MMDavito/8_switch_rgb/KiCad/8_switch_rgb_pcb_revision_1/3D_no_grund_plane.png

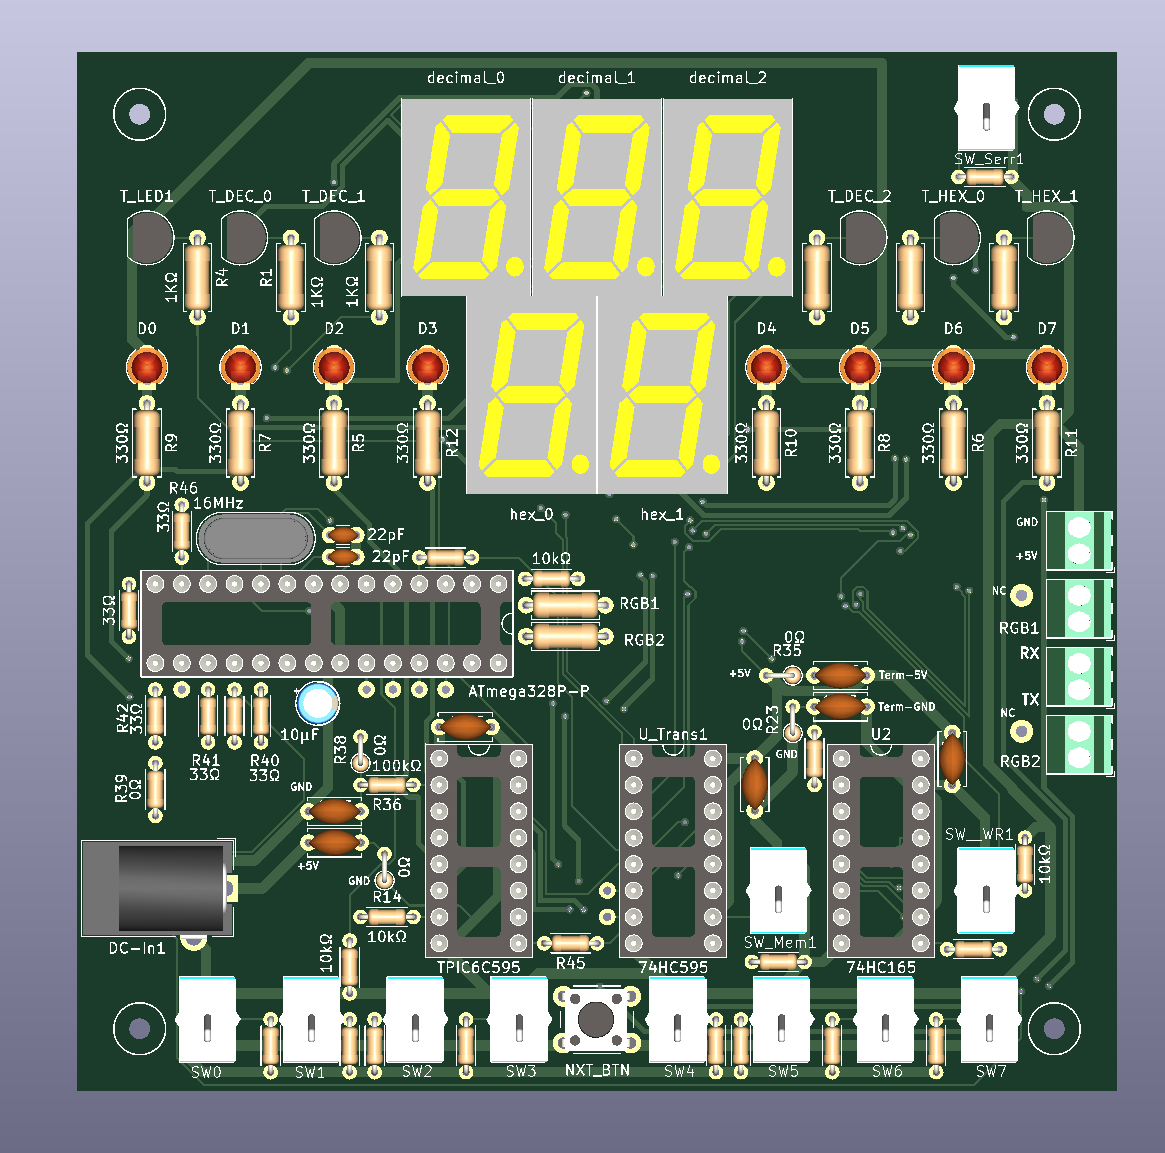
KiCad/8_switch_rgb_pcb_revision_1/3D_no_grund_plane.png
