MMDavito/8_switch_rgb/KiCad/8_switch_rgb_pcb_revision_1/After connections and DRC awful, but cleaner.png

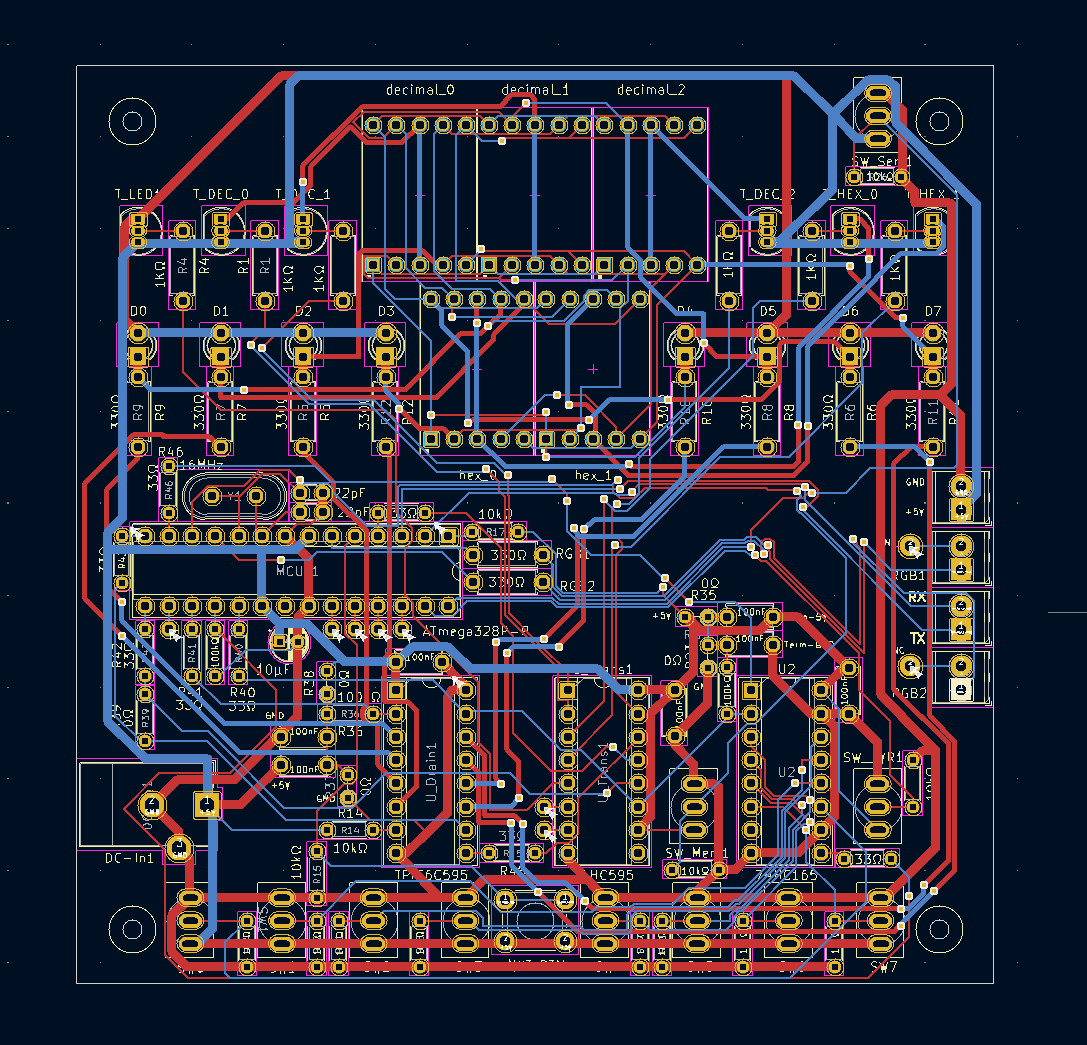
KiCad/8_switch_rgb_pcb_revision_1/After connections and DRC awful, but cleaner.png
