MMDavito/8_switch_rgb/KiCad/8_switch_rgb_pcb_revision_1/BlackMagic v2.png

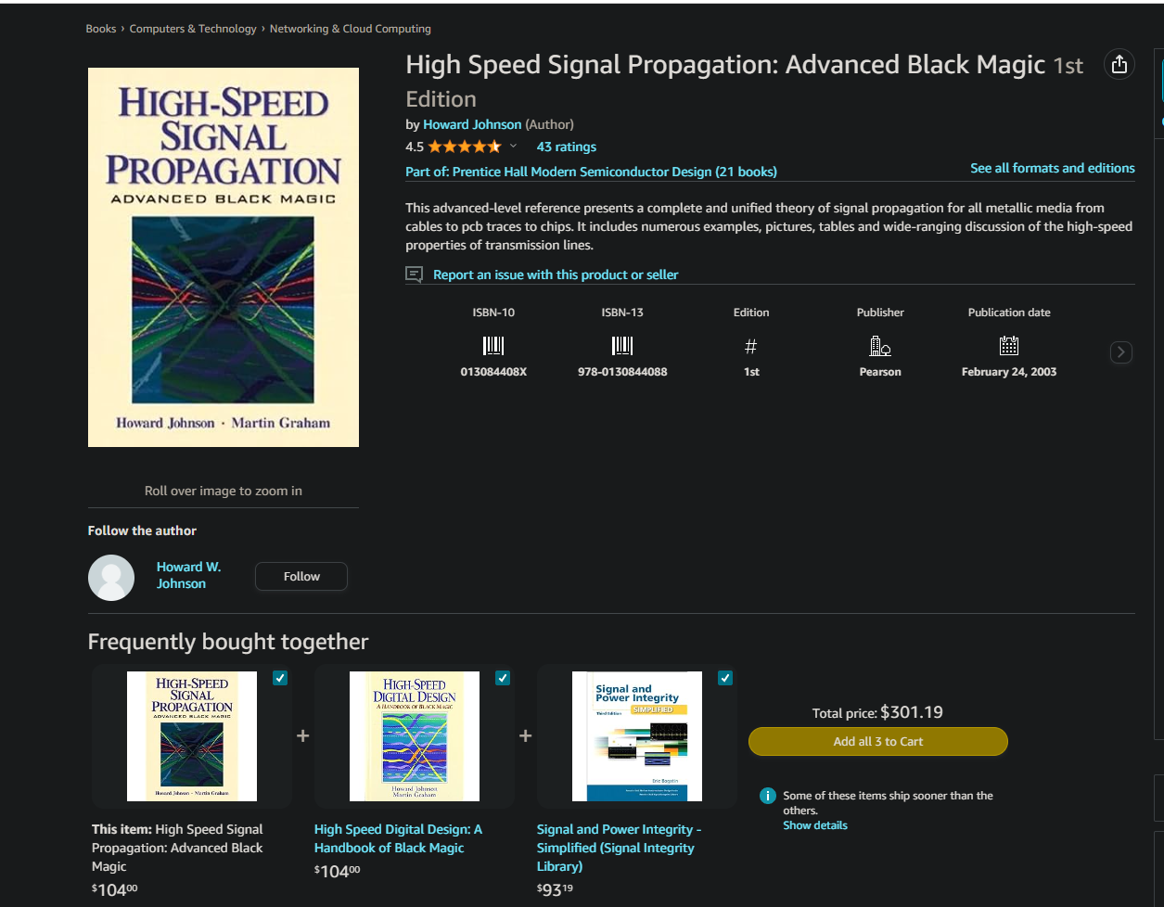
KiCad/8_switch_rgb_pcb_revision_1/BlackMagic v2.png
