MMDavito/8_switch_rgb/KiCad/8_switch_rgb_pcb_revision_1/NotLogicOffset_rev0.png

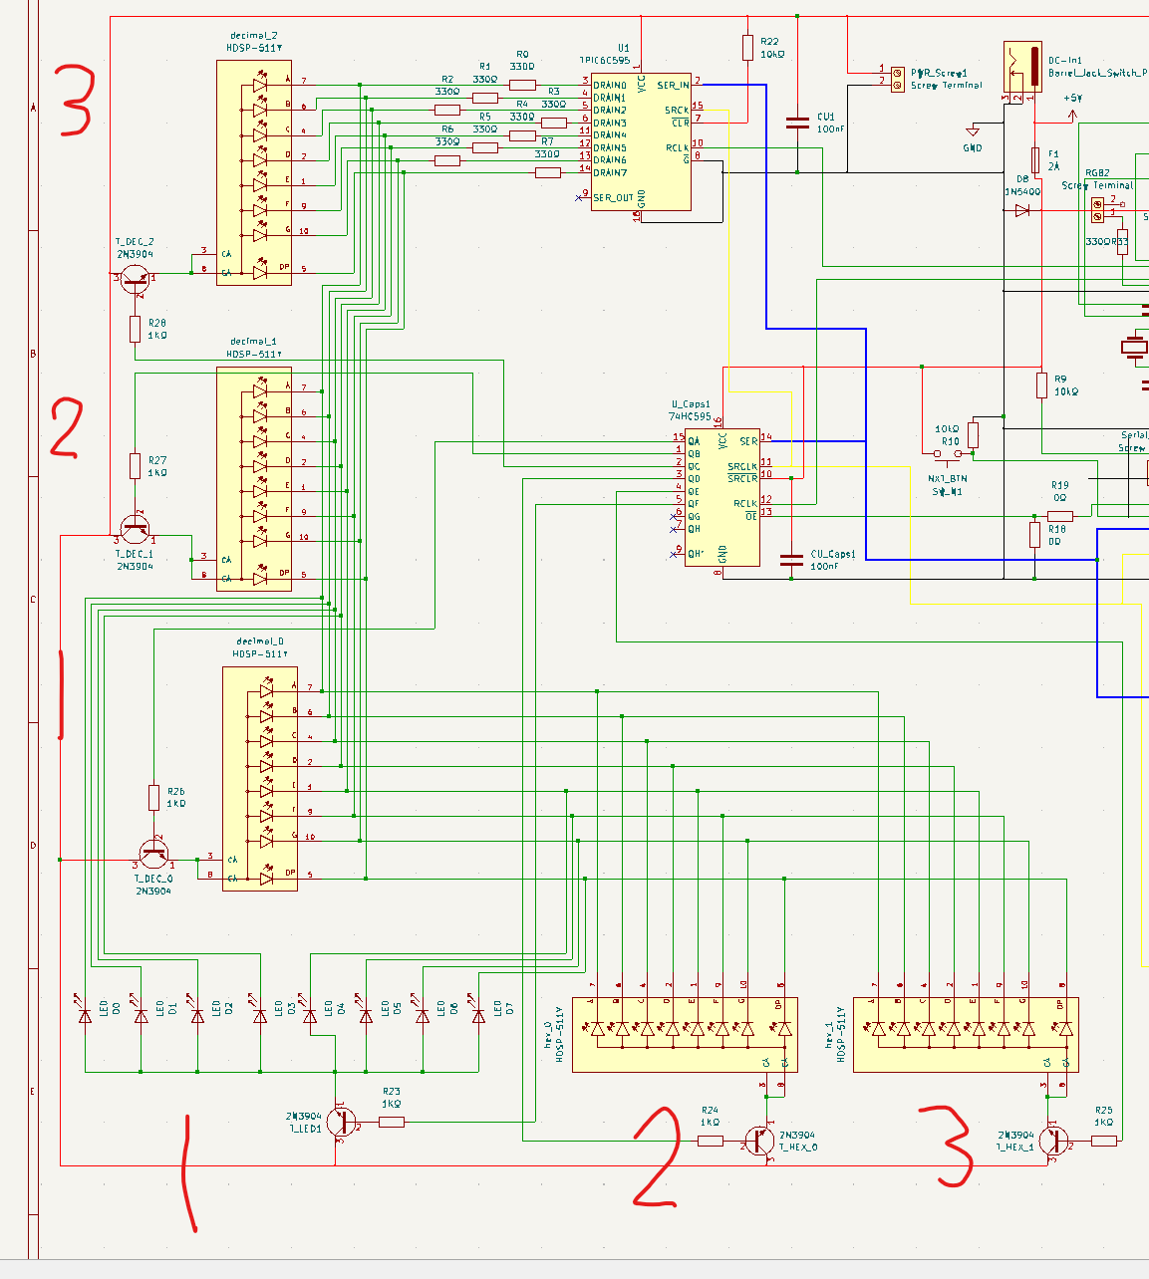
KiCad/8_switch_rgb_pcb_revision_1/NotLogicOffset_rev0.png
