MMDavito/8_switch_rgb/KiCad/12x12CM.png

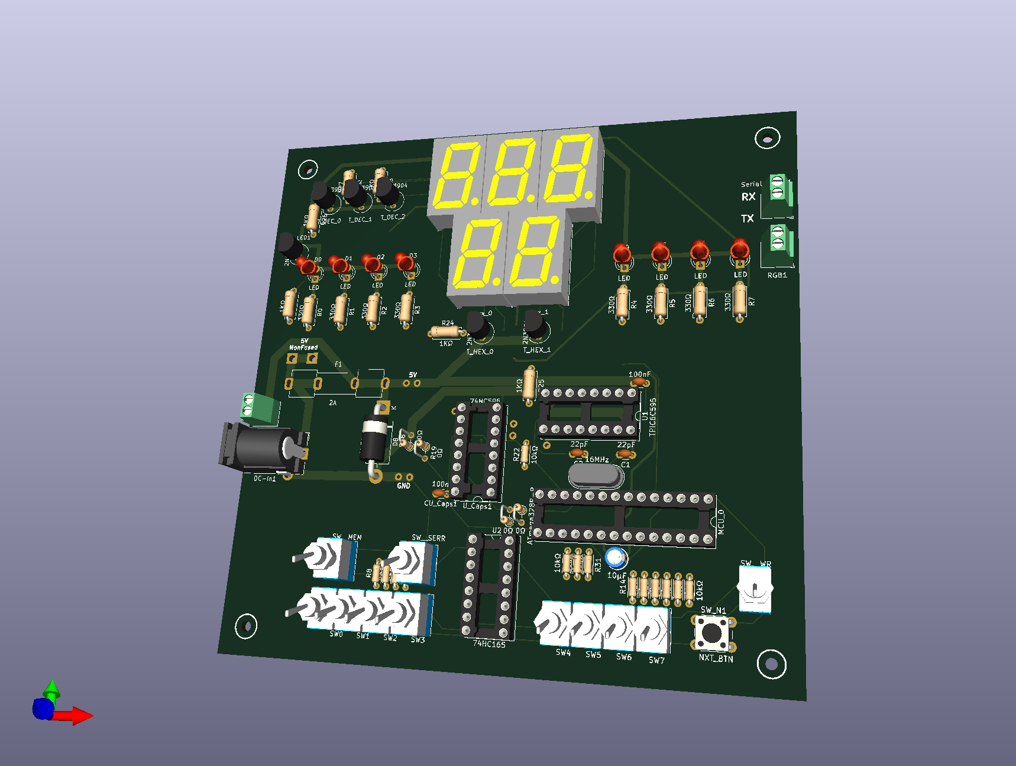
KiCad/12x12CM.png
