MMDavito/8_switch_rgb/KiCad/flip_flop/NAND_gates force using arduino to Pull SWITCH SET High when Reset ensure resistors ensure trigger level.png

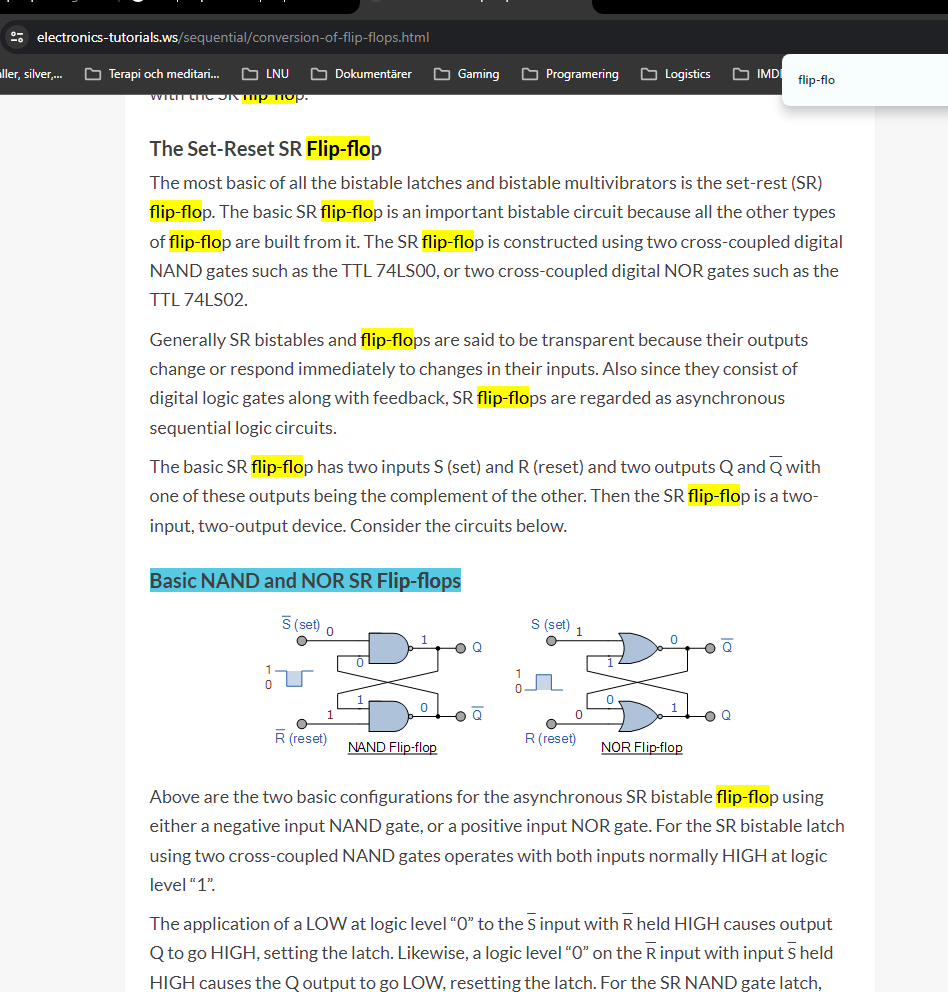
KiCad/flip_flop/NAND_gates force using arduino to Pull SWITCH SET High when Reset ensure resistors ensure trigger level.png
