MMDavito/8_switch_rgb/KiCad/flip_flop/schmit_trigger.png

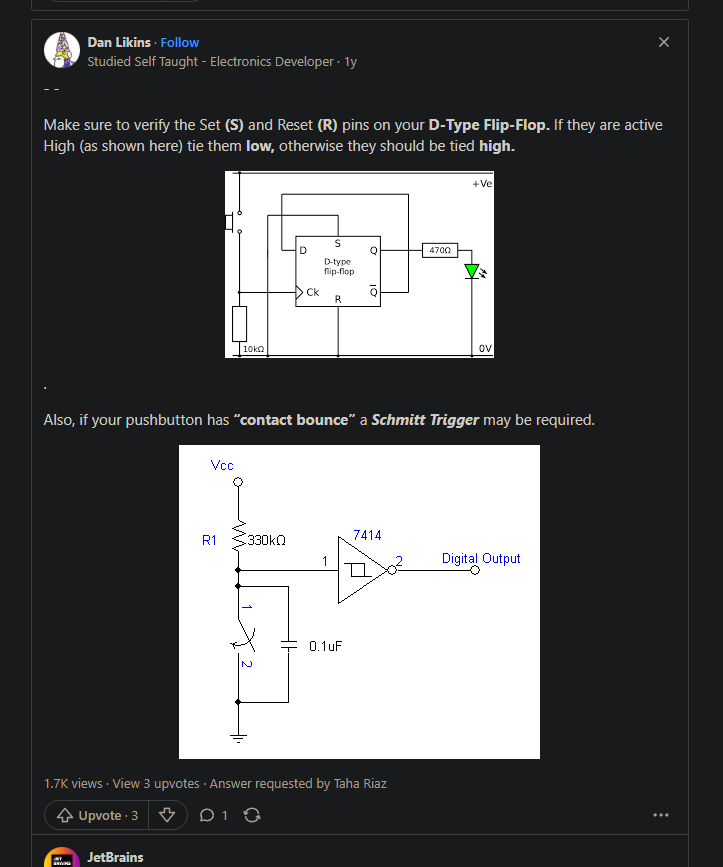
KiCad/flip_flop/schmit_trigger.png
