MMDavito/8_switch_rgb/KiCad/PCB_JPEG.jpg

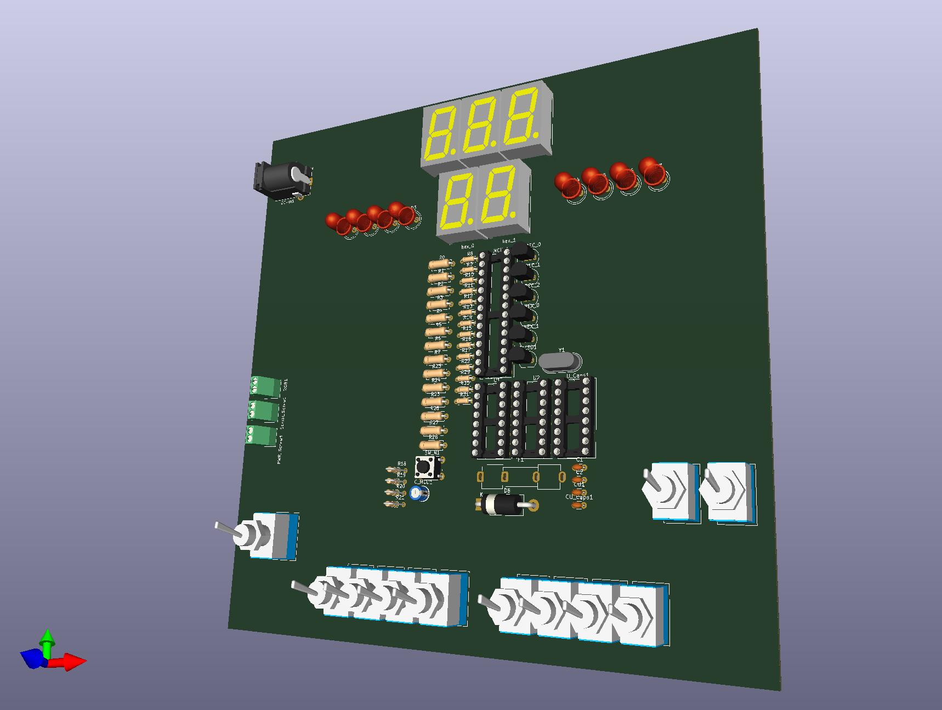
KiCad/PCB_JPEG.jpg
