MMDavito/8_switch_rgb/KiCad/pcbTracev1.png

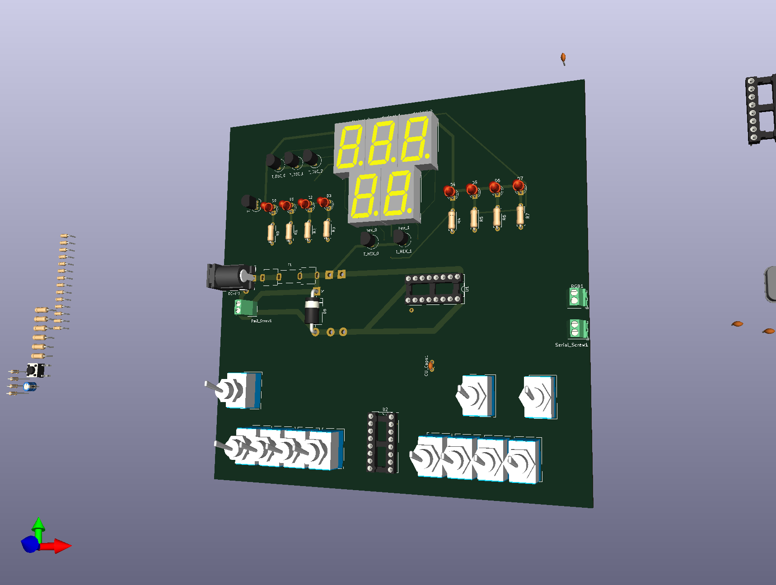
KiCad/pcbTracev1.png
