MMDavito/8_switch_rgb/KiCad/pcbTracev1_back.png

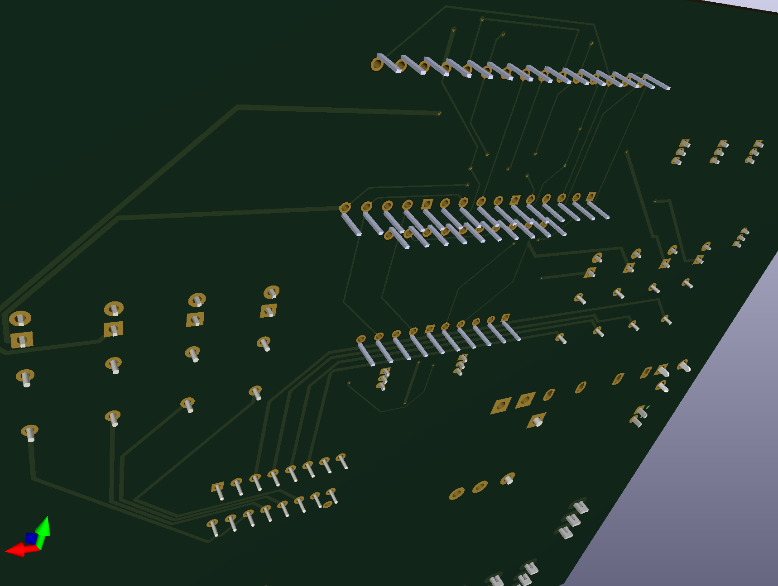
KiCad/pcbTracev1_back.png
