MMDavito/8_switch_rgb/KiCad/Solving_Sum_Violations.png

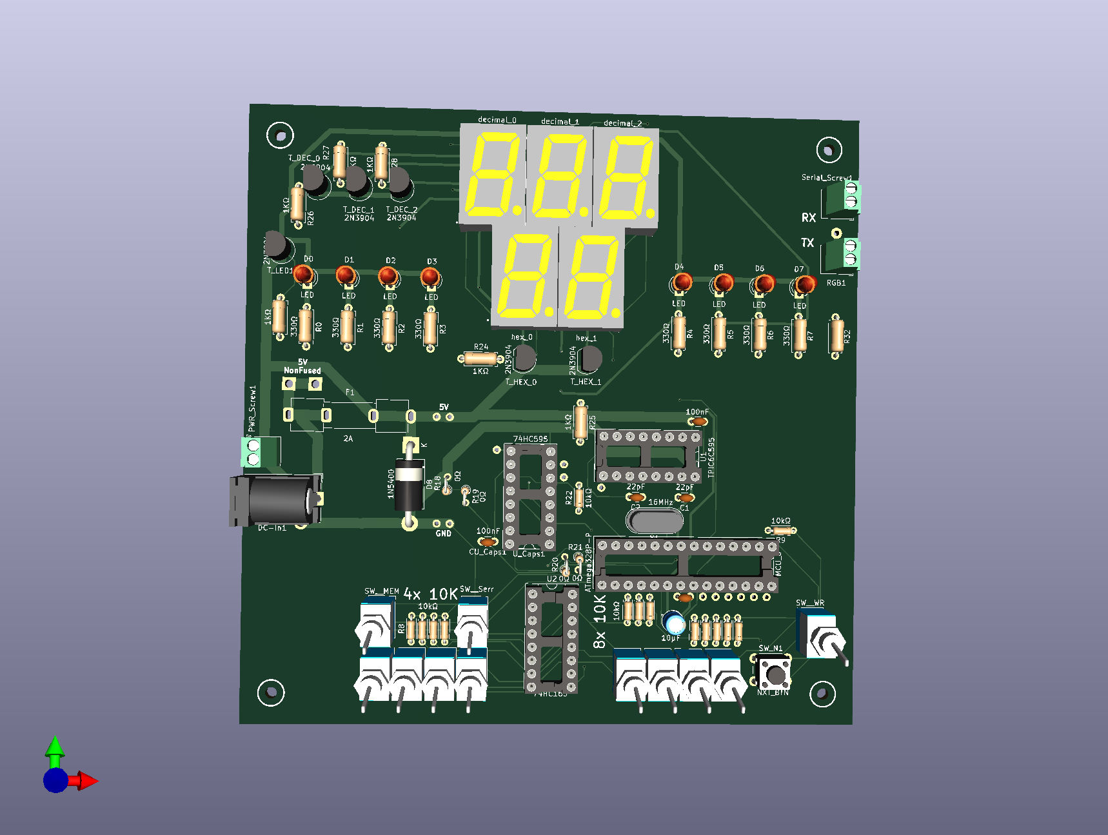
KiCad/Solving_Sum_Violations.png
