MMDavito/8_switch_rgb/FreeCad/holders/2-7mm_pocket_hex_1mm_bottom.stl

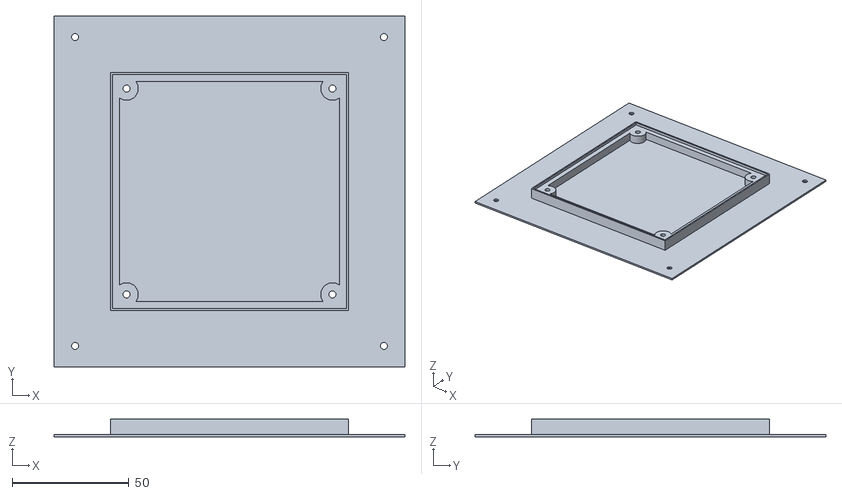
[picture p46: CAD file, 2024-03-04]
FreeCad/holders/2-7mm_pocket_hex_1mm_bottom.stl
150.0 x 150.0 x 7.60
