MMDavito/8_switch_rgb/FreeCad/assembling_tools/resistor_bending_tool.FCStd

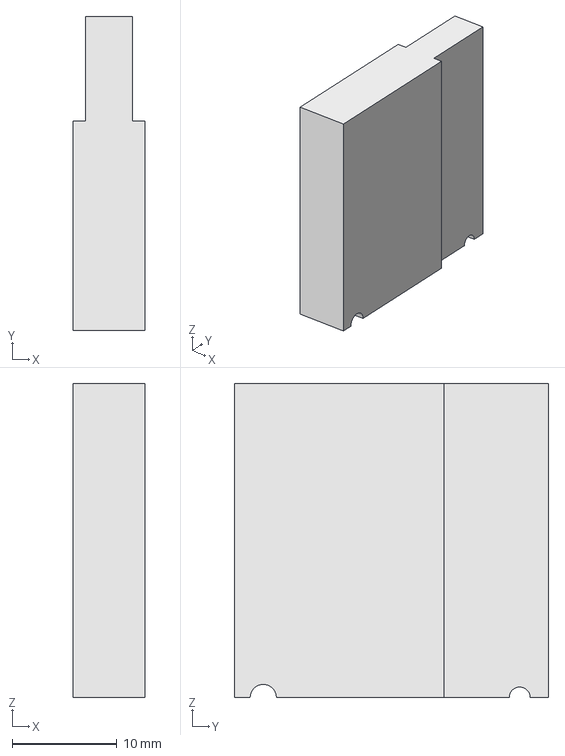
[picture p47: CAD file, 2024-03-13]
FreeCad/assembling_tools/resistor_bending_tool.FCStd
6.90 x 30.0 x 30.0 mm
