MMDavito/8_switch_rgb/FreeCad/holders/1mm_bottom_pads_for_button_and_mcu.stl

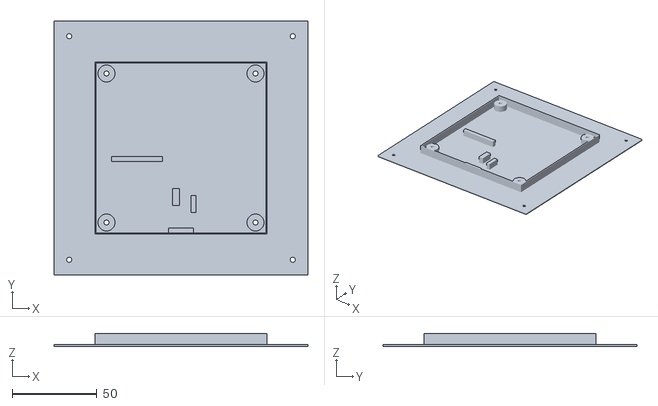
[picture p48: CAD file, 2024-03-04]
FreeCad/holders/1mm_bottom_pads_for_button_and_mcu.stl
150.0 x 150.0 x 7.60
