MMDavito/8_switch_rgb/FreeCad/holders/5_mm_inc_pcb.stl

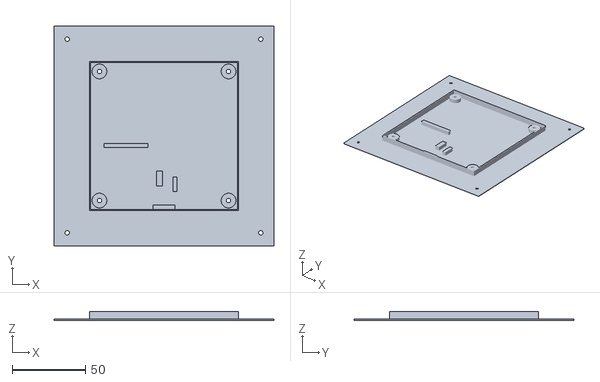
[picture p49: CAD file, 2024-03-04]
FreeCad/holders/5_mm_inc_pcb.stl
150.0 x 150.0 x 6.00
