MMDavito/8_switch_rgb/FreeCad/holders/only_pocket.step

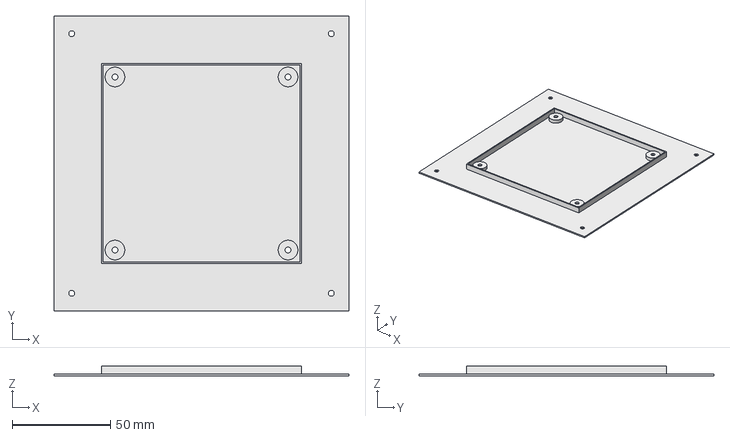
[picture p50: CAD file, 2024-03-04]
FreeCad/holders/only_pocket.step
150.0 x 150.0 x 5.10 mm
